ILunaA/MWS/20170422_MWStrip/Screenshot_2017-04-23-11-54-00.jpeg

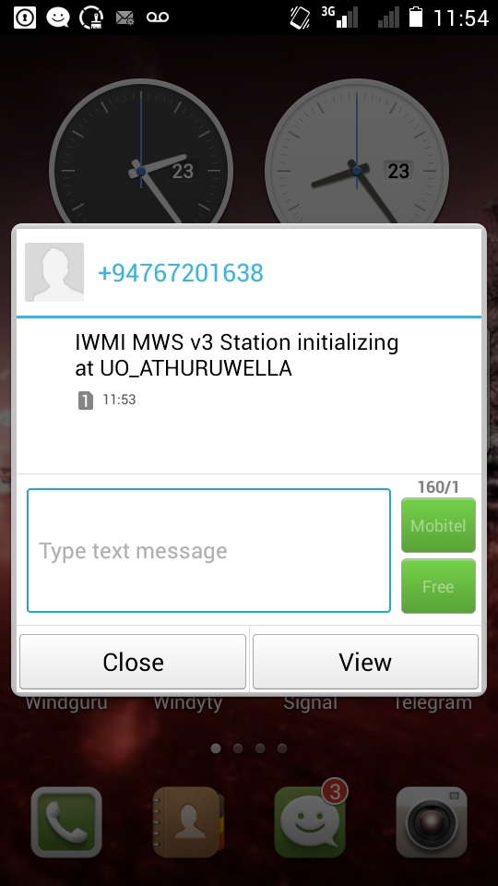
20170422_MWStrip/Screenshot_2017-04-23-11-54-00.jpeg
