ILunaA/MWS/20170422_MWStrip/Screenshot_2017-04-25-07-33-01.jpeg

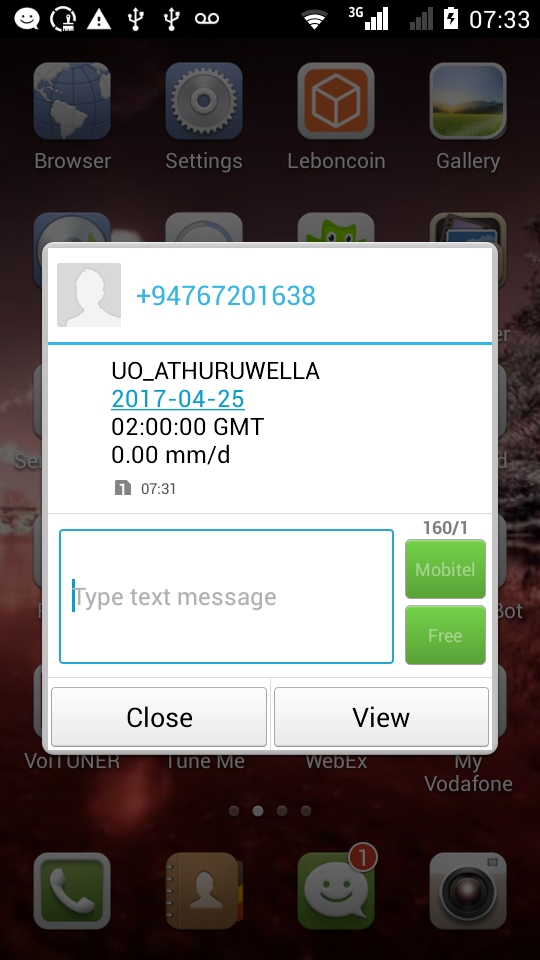
20170422_MWStrip/Screenshot_2017-04-25-07-33-01.jpeg
