ILunaA/MWS/20170422_MWStrip/Screenshot_2017-04-25-11-26-05.jpeg

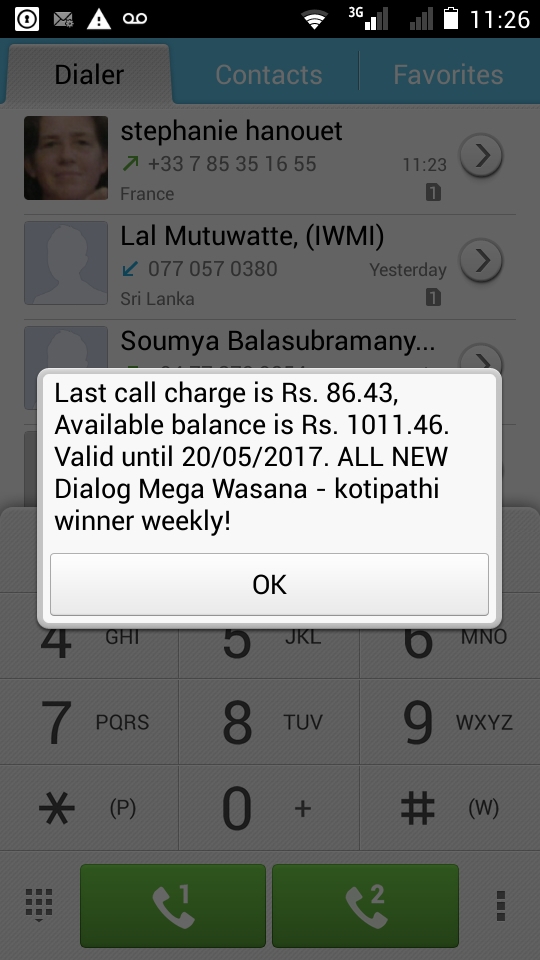
20170422_MWStrip/Screenshot_2017-04-25-11-26-05.jpeg
