ILunaA/MWS/20170422_MWStrip/Screenshot_2017-04-25-14-49-04.jpeg

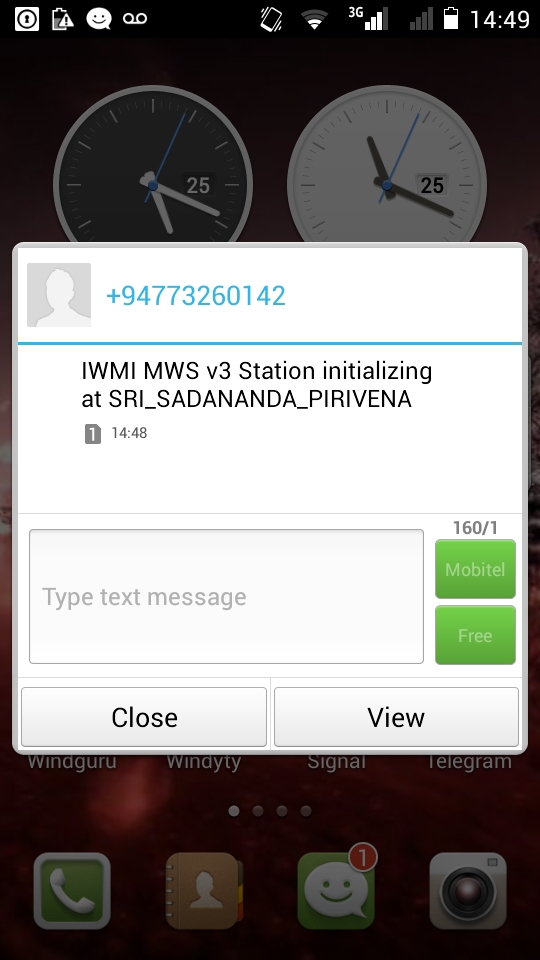
20170422_MWStrip/Screenshot_2017-04-25-14-49-04.jpeg
