ILunaA/MWS/20170422_MWStrip/Screenshot_2017-04-25-15-38-25.jpeg

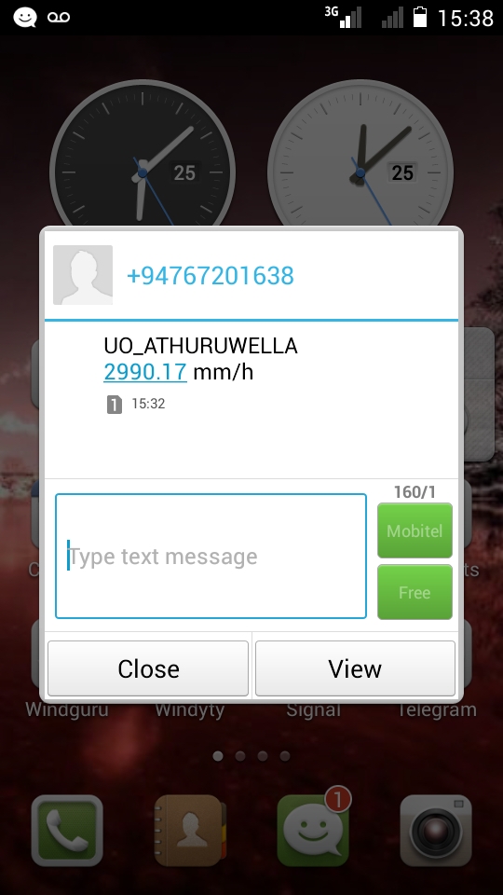
20170422_MWStrip/Screenshot_2017-04-25-15-38-25.jpeg
