ILunaA/MWS/20170422_MWStrip/Screenshot_2017-04-25-21-17-44.jpeg

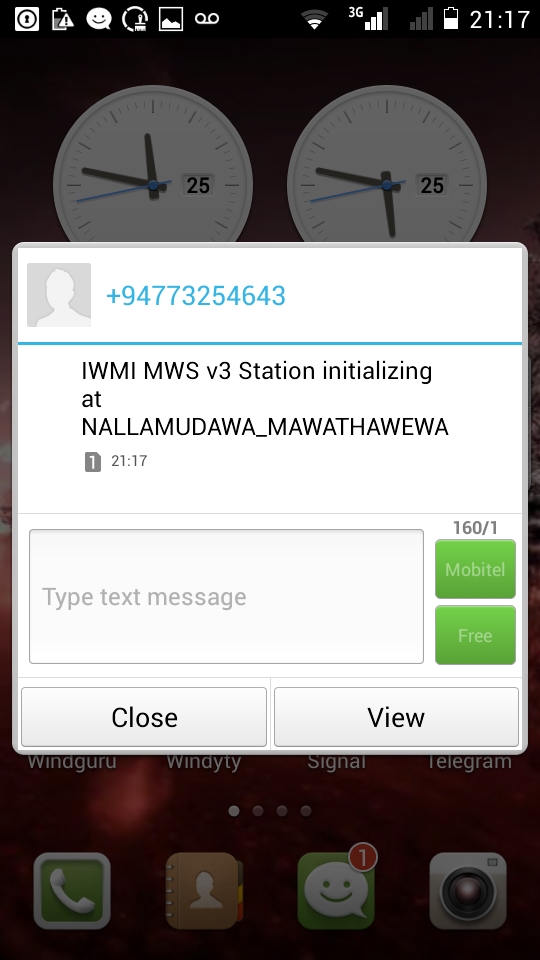
20170422_MWStrip/Screenshot_2017-04-25-21-17-44.jpeg
