ILunaA/MWS/DATA/UO_PALAYAKULAMA/MWSDataAnalysis.png

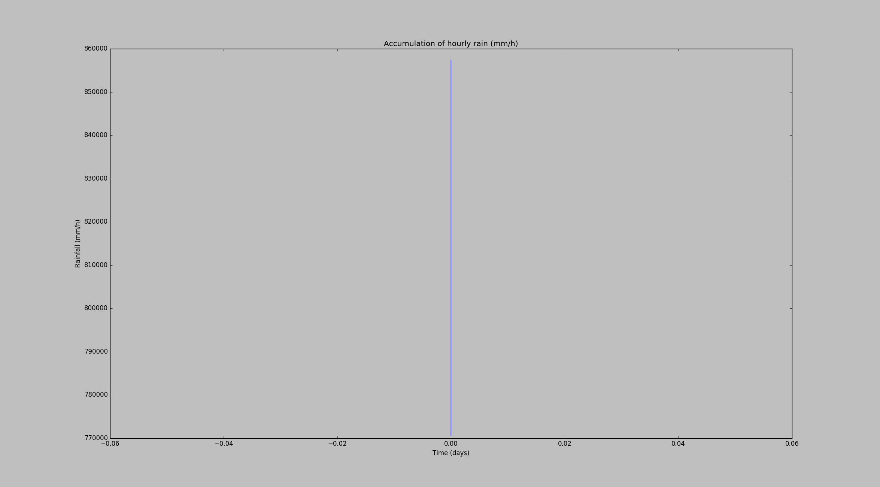
DATA/UO_PALAYAKULAMA/MWSDataAnalysis.png
