ILunaA/MWS/OSHW/radiationshield/Screen Shot 2015-04-08 at 9.11.47 PM.png

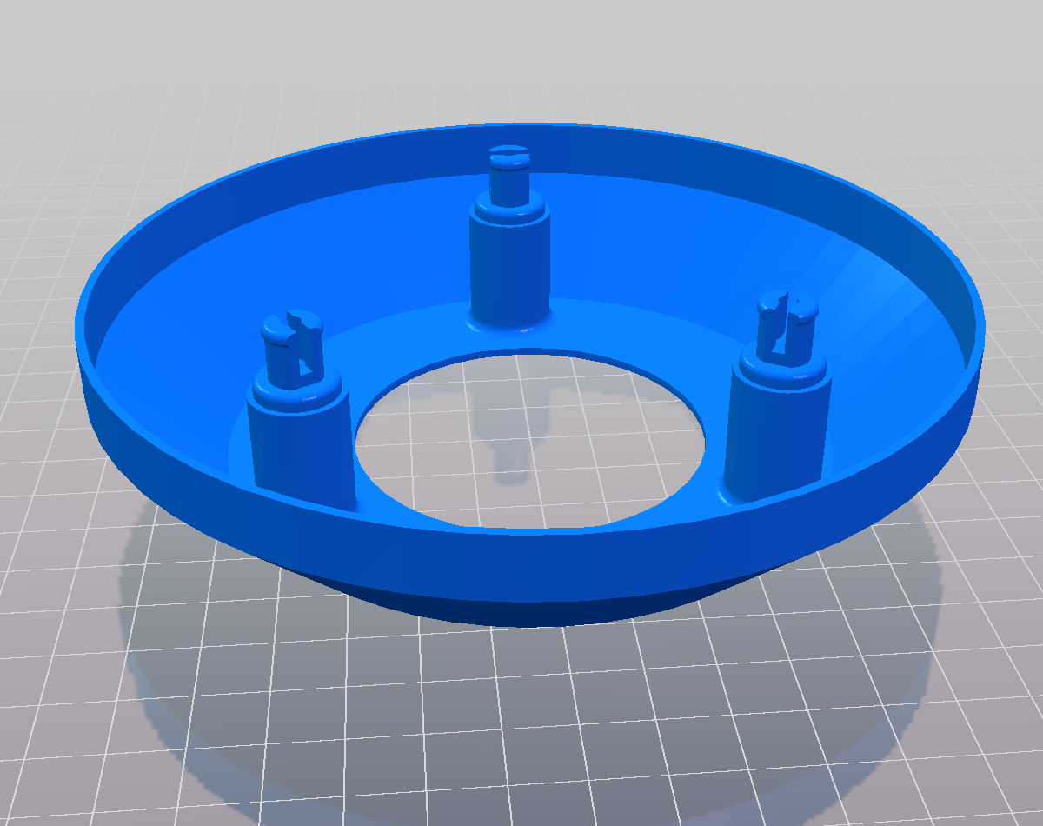
OSHW/radiationshield/Screen Shot 2015-04-08 at 9.11.47 PM.png
