ILunaA/MWS/OSHW/radiationshield/Screen Shot 2015-04-08 at 9.12.31 PM.png

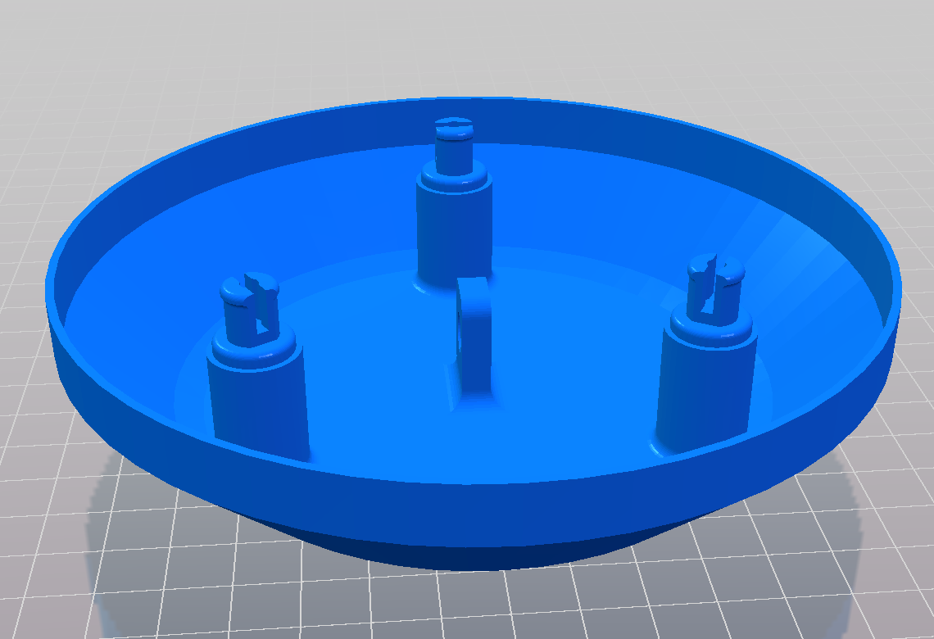
OSHW/radiationshield/Screen Shot 2015-04-08 at 9.12.31 PM.png
