ILunaA/MWS/OSHW/raingauge2/rainmeter_display_large_preview_featured.jpg

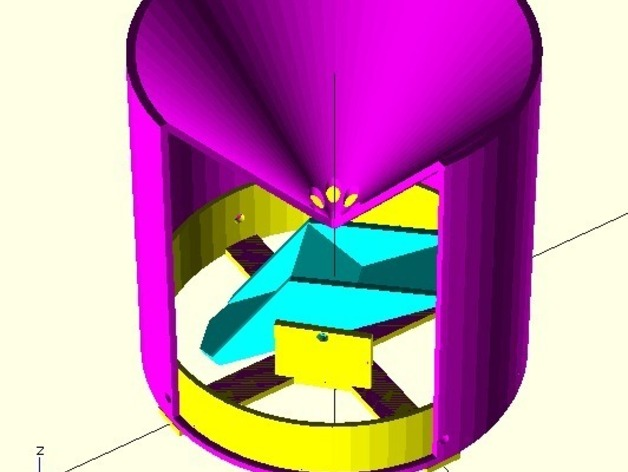
OSHW/raingauge2/rainmeter_display_large_preview_featured.jpg
