ILunaA/MWS/OSHW/raingauge2/rainmeter_plate_lowres_preview_featured.jpg

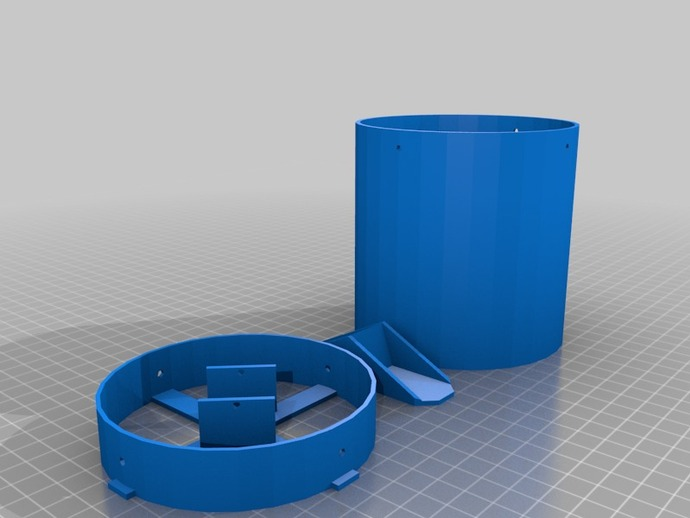
OSHW/raingauge2/rainmeter_plate_lowres_preview_featured.jpg
