ILunaA/MWS/OSHW/raingauge2/rainmeter_preview_featured.jpg

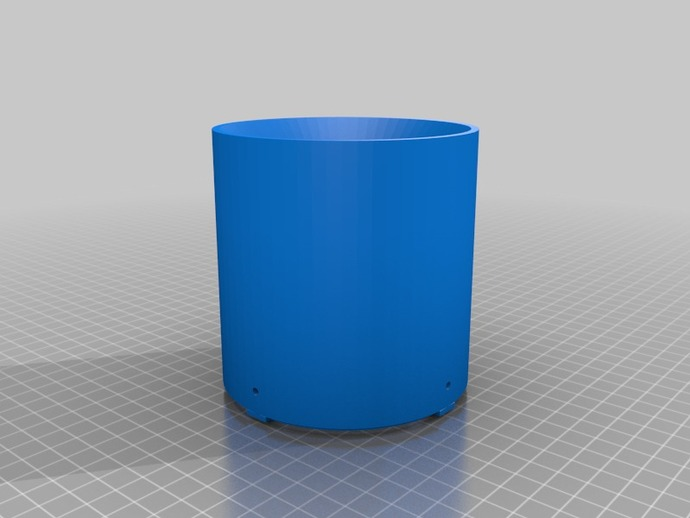
OSHW/raingauge2/rainmeter_preview_featured.jpg
