ILunaA/MWS/OSHW/raingauge3_windspeed/Screenshot from 2016-06-08 13-36-43.png

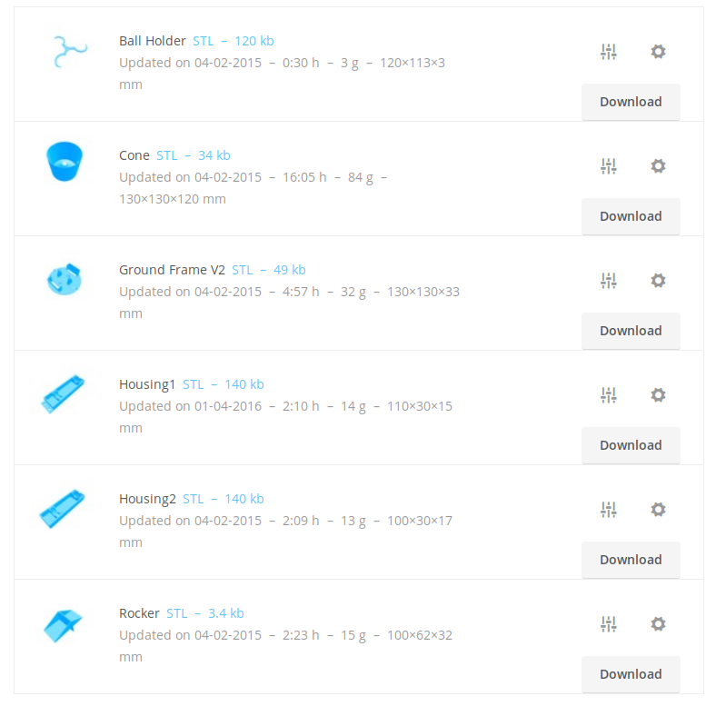
OSHW/raingauge3_windspeed/Screenshot from 2016-06-08 13-36-43.png
