ILunaA/MWS/OSHW/raingauge/Assem2round2.JPG

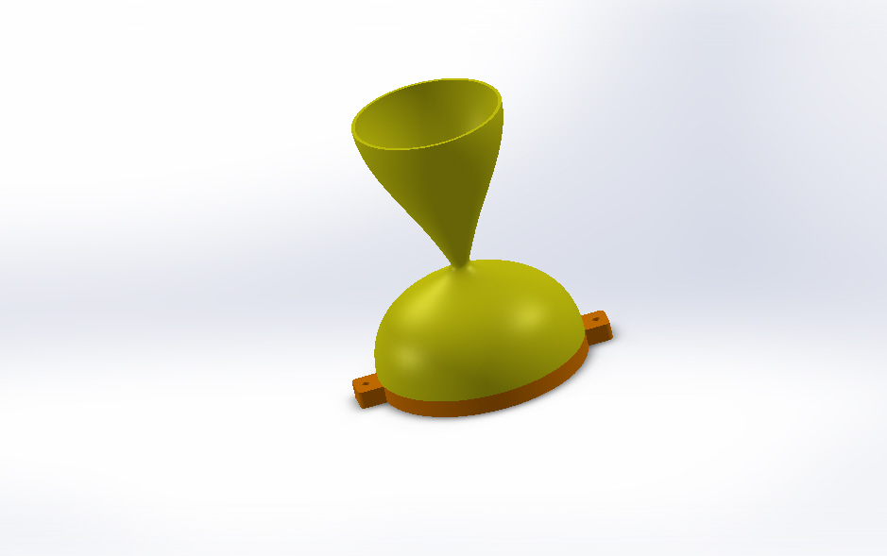
OSHW/raingauge/Assem2round2.JPG
