ILunaA/MWS/OSHW/raingauge/base-round.JPG

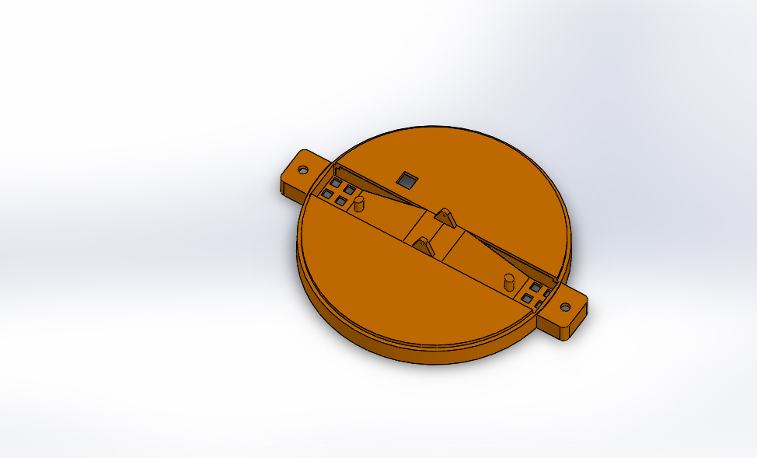
OSHW/raingauge/base-round.JPG
