ILunaA/MWS/OSHW/raingauge/collector - Copyround.JPG

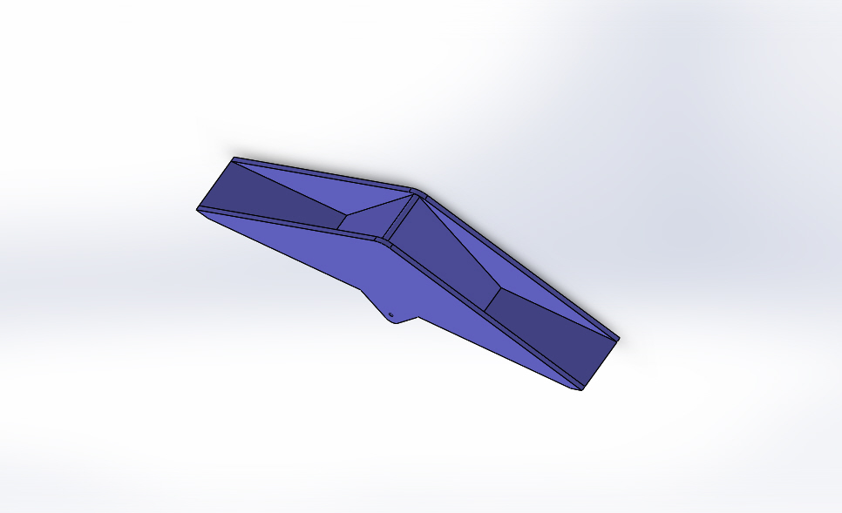
OSHW/raingauge/collector - Copyround.JPG
