ILunaA/MWS/OSHW/raingauge/Cover-round1.JPG

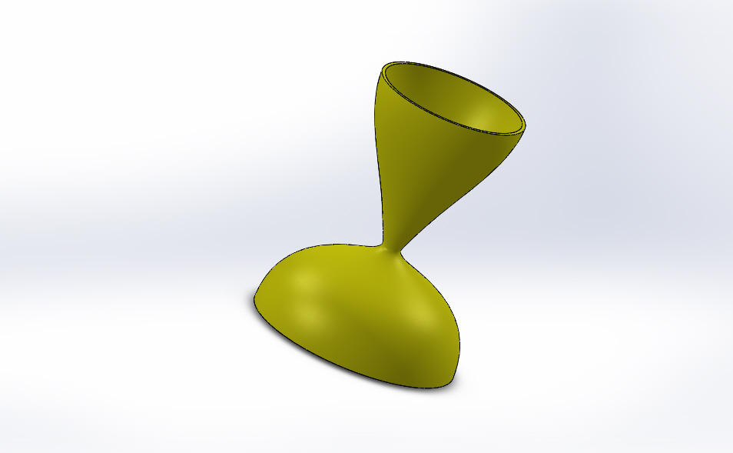
OSHW/raingauge/Cover-round1.JPG
