ILunaA/MWS/OSHW/raingauge/Cover-round.JPG

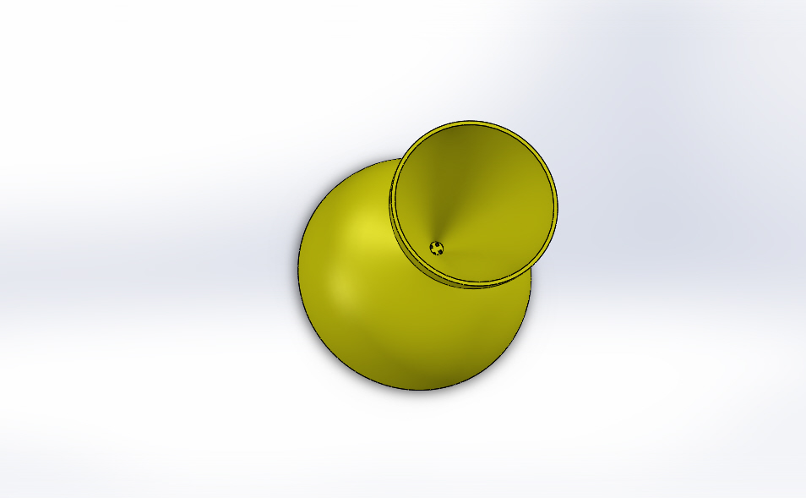
OSHW/raingauge/Cover-round.JPG
