ILunaA/MWS/OSHW/raingauge3_windspeed/ground_frame_v2.stl

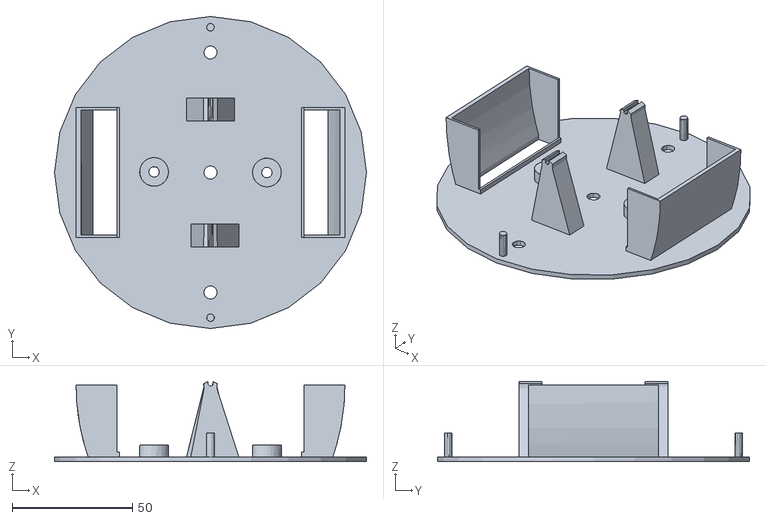
[picture p48: CAD file, 2016-06-08]
OSHW/raingauge3_windspeed/ground_frame_v2.stl
130.0 x 130.0 x 33.4
