ILunaA/MWS/OSHW/raingauge4/files/Outer_Body.stl

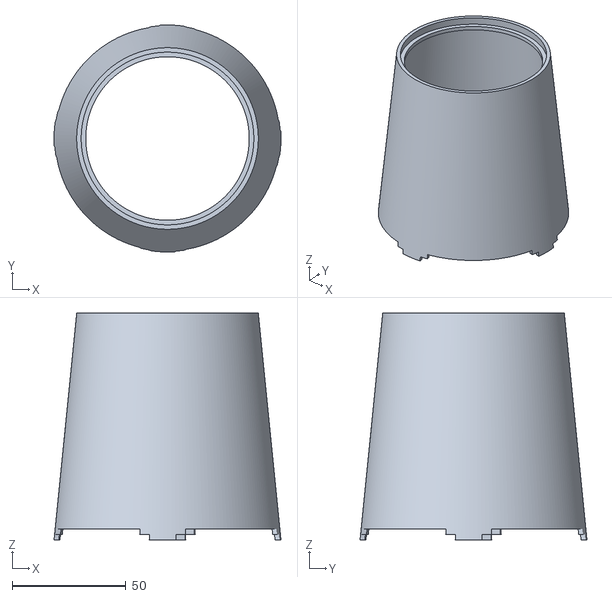
[picture p49: CAD file, 2017-03-09]
OSHW/raingauge4/files/Outer_Body.stl
100.0 x 100.0 x 100.0
