ILunaA/MWS/OSHW/Pluviometro/BOTTOM CAP.SLDPRT

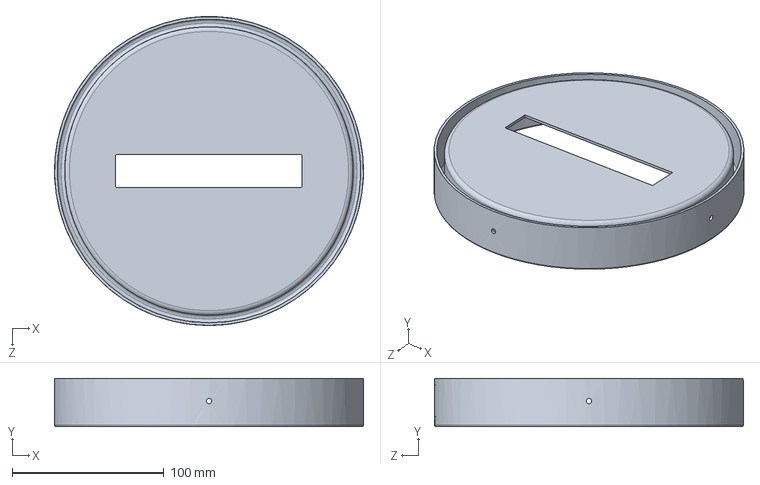
[picture p50: CAD file, 2017-05-09]
OSHW/Pluviometro/BOTTOM CAP.SLDPRT
203.6 x 31.8 x 203.6 mm
