ILunaA/MWS/OSHW/radiationshield1/Radiation_Shield_For_Weather_Station_Temperature_Humidity/Rad_Shd_Fin_V1.stl

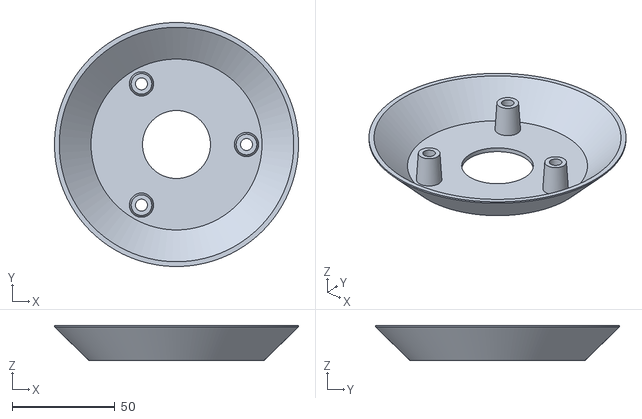
[picture p51: CAD file, 2016-03-31]
OSHW/radiationshield1/Radiation_Shield_For_Weather_Station_Temperature_Humidity/Rad_Shd_Fin_V1.stl
118.5 x 118.5 x 17.0
