ILunaA/MWS/OSHW/raingauge/base-round.SLDPRT

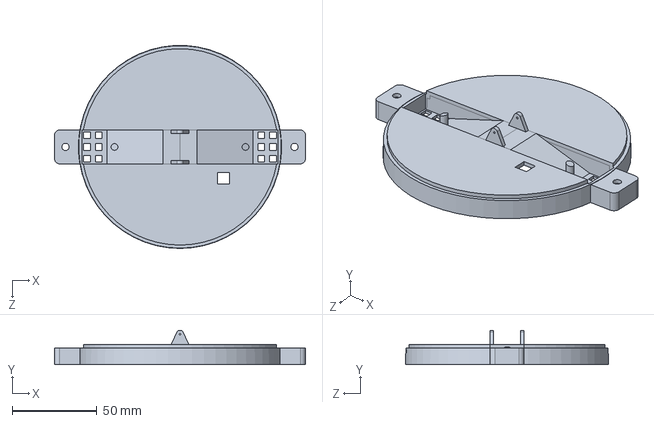
[picture p52: CAD file, 2015-03-08]
OSHW/raingauge/base-round.SLDPRT
148.3 x 20.4 x 119.9 mm
