ILunaA/MWS/OSHW/raingauge1/rain_base2.stl

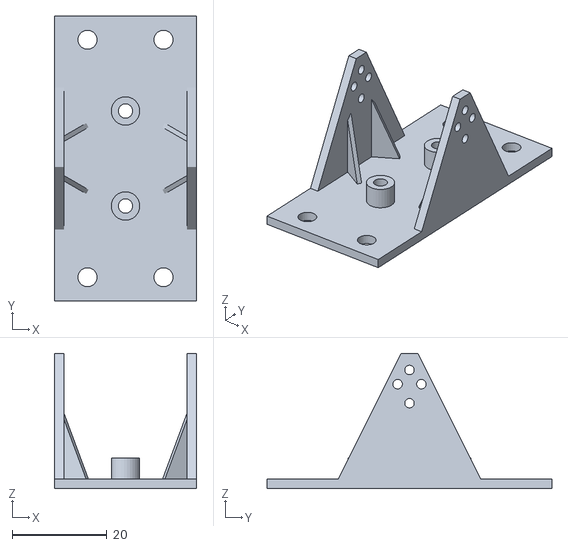
[picture p53: CAD file, 2015-04-08]
OSHW/raingauge1/rain_base2.stl
30.0 x 60.0 x 28.5
