ILunaA/MWS/OSHW/raingauge3_windspeed/cone.stl

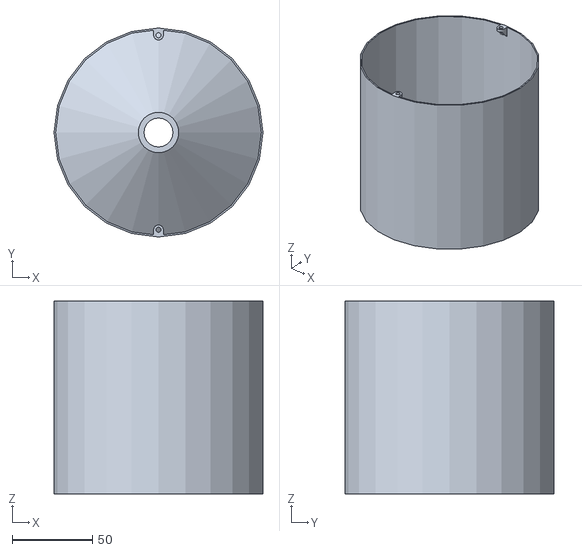
[picture p54: CAD file, 2016-06-08]
OSHW/raingauge3_windspeed/cone.stl
130.0 x 130.0 x 120.0
