ILunaA/MWS/OSHW/raingauge4/files/Funnel.stl

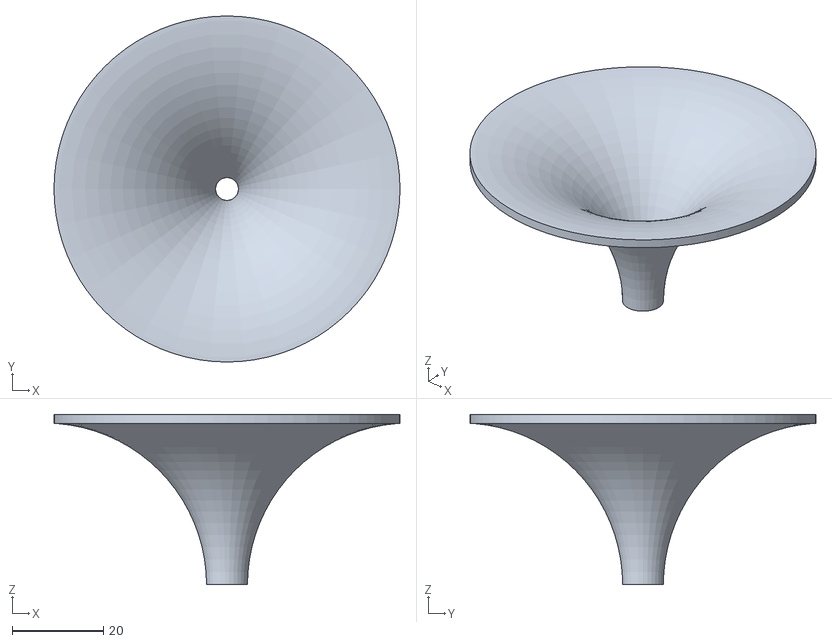
[picture p55: CAD file, 2017-03-09]
OSHW/raingauge4/files/Funnel.stl
76.0 x 76.0 x 37.4
