ILunaA/MWS/OSHW/Pluviometro/Tic.SLDPRT

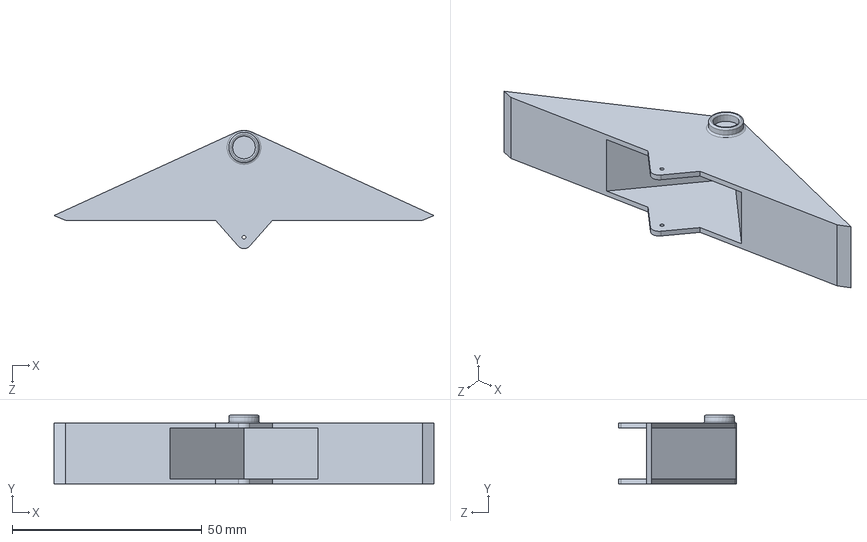
[picture p56: CAD file, 2017-05-09]
OSHW/Pluviometro/Tic.SLDPRT
100.0 x 18.1 x 31.1 mm
