ILunaA/MWS/OSHW/radiationshield1/Radiation_Shield_For_Weather_Station_Temperature_Humidity/AM2315_mount_V1.stl

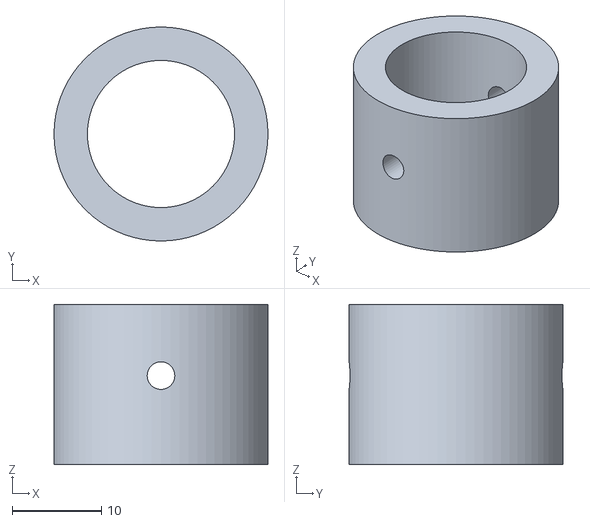
[picture p57: CAD file, 2016-03-31]
OSHW/radiationshield1/Radiation_Shield_For_Weather_Station_Temperature_Humidity/AM2315_mount_V1.stl
24.0 x 24.0 x 18.0
