ILunaA/MWS/OSHW/raingauge/Assem2.STEP

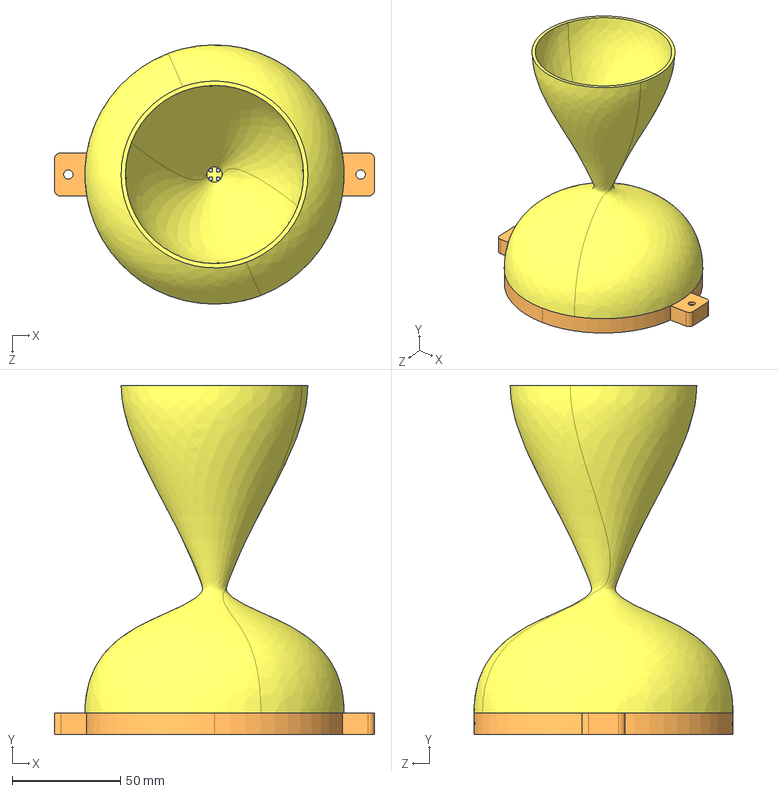
[picture p58: CAD file, 2015-03-08]
OSHW/raingauge/Assem2.STEP
148.3 x 161.5 x 120.0 mm
base-round
collector - Copy
Cover-round
