ILunaA/MWS/OSHW/raingauge1/Base3.stl

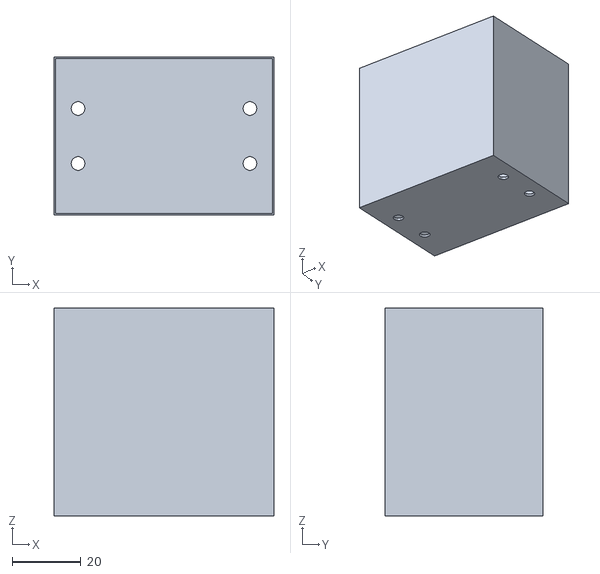
[picture p59: CAD file, 2015-04-08]
OSHW/raingauge1/Base3.stl
64.0 x 46.0 x 60.5
