ILunaA/MWS/OSHW/raingauge3_windspeed/ball_holder.stl

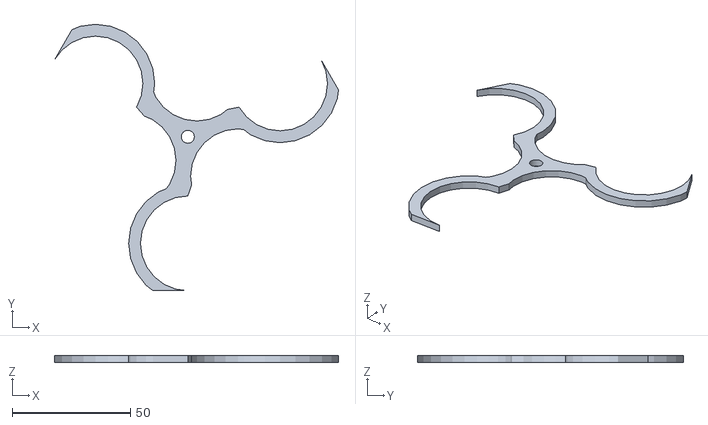
[picture p60: CAD file, 2016-06-08]
OSHW/raingauge3_windspeed/ball_holder.stl
119.9 x 112.5 x 3.00
