ILunaA/MWS/OSHW/raingauge4/files/Base.stl

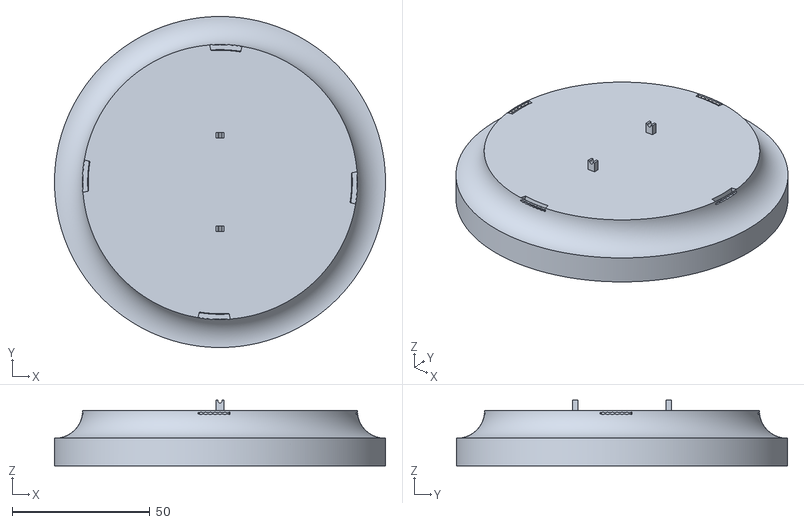
[picture p61: CAD file, 2017-03-09]
OSHW/raingauge4/files/Base.stl
120.0 x 120.0 x 23.8
