ILunaA/MWS/OSHW/radiationshield1/Radiation_Shield_For_Weather_Station_Temperature_Humidity/Rad_Shd_Horz_mount_V1.stl

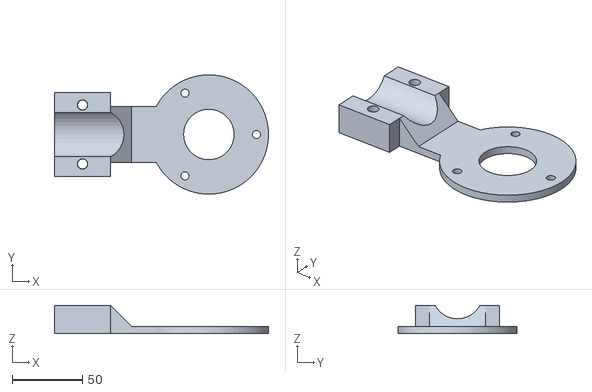
[picture p62: CAD file, 2016-03-31]
OSHW/radiationshield1/Radiation_Shield_For_Weather_Station_Temperature_Humidity/Rad_Shd_Horz_mount_V1.stl
152.5 x 85.0 x 20.0
