ILunaA/MWS/OSHW/raingauge3_windspeed/housing1.stl

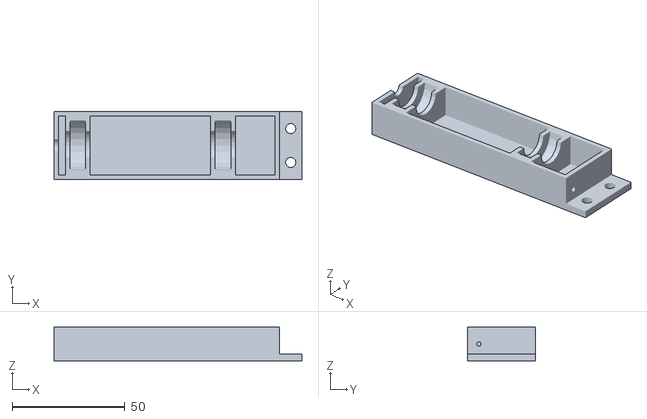
[picture p63: CAD file, 2016-06-08]
OSHW/raingauge3_windspeed/housing1.stl
110.0 x 30.0 x 15.0
