ILunaA/MWS/OSHW/Pluviometro/SPACER.SLDPRT

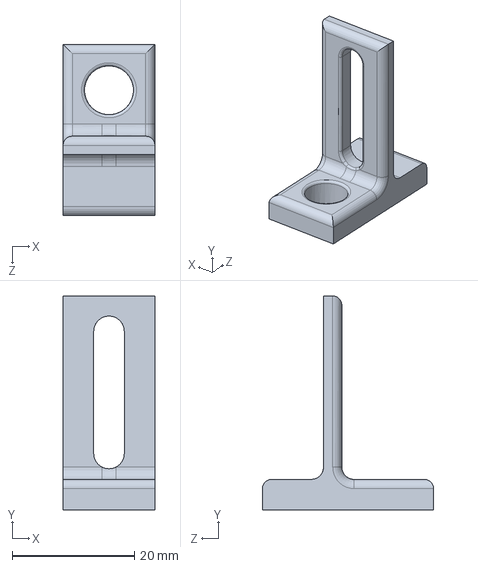
[picture p64: CAD file, 2017-05-09]
OSHW/Pluviometro/SPACER.SLDPRT
15.0 x 35.0 x 28.0 mm
