ILunaA/MWS/OSHW/radiationshield1/Radiation_Shield_For_Weather_Station_Temperature_Humidity/SHT15_mount_V1.stl

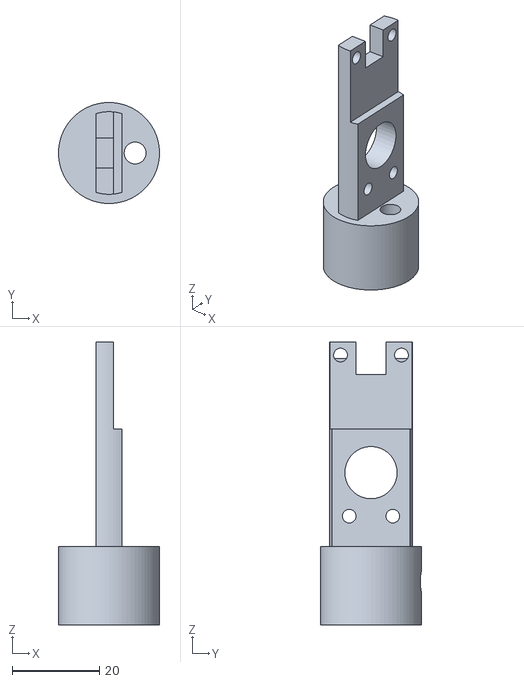
[picture p65: CAD file, 2016-03-31]
OSHW/radiationshield1/Radiation_Shield_For_Weather_Station_Temperature_Humidity/SHT15_mount_V1.stl
23.2 x 23.2 x 65.0
