ILunaA/MWS/OSHW/raingauge3_windspeed/rocker.stl

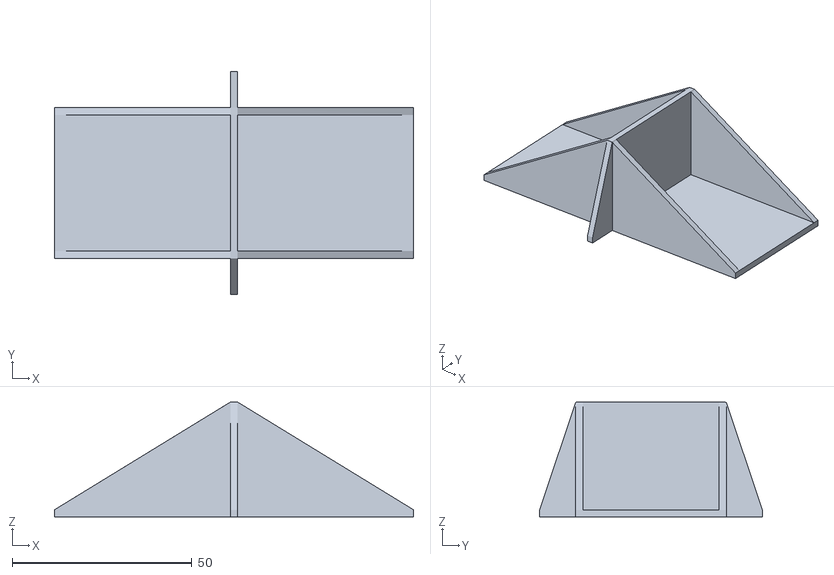
[picture p66: CAD file, 2016-06-08]
OSHW/raingauge3_windspeed/rocker.stl
100.0 x 62.0 x 32.0
