ILunaA/MWS/OSHW/Pluviometro/SUPPORT.SLDPRT

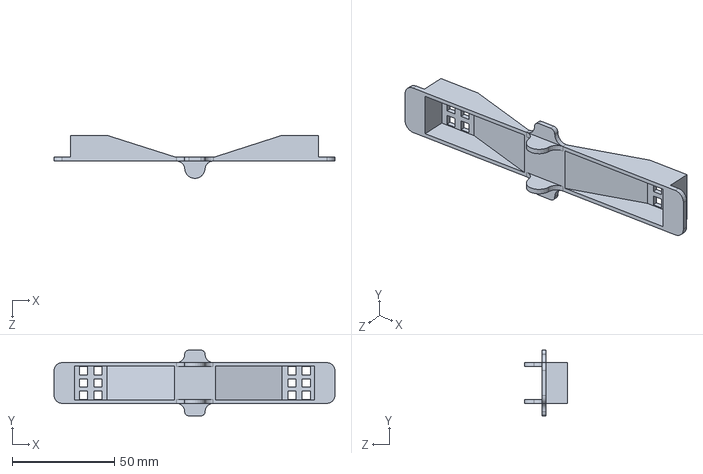
[picture p67: CAD file, 2017-05-09]
OSHW/Pluviometro/SUPPORT.SLDPRT
137.6 x 32.2 x 21.0 mm
