ILunaA/MWS/OSHW/radiationshield1/Radiation_Shield_For_Weather_Station_Temperature_Humidity/HTU21D_mount_V1.stl

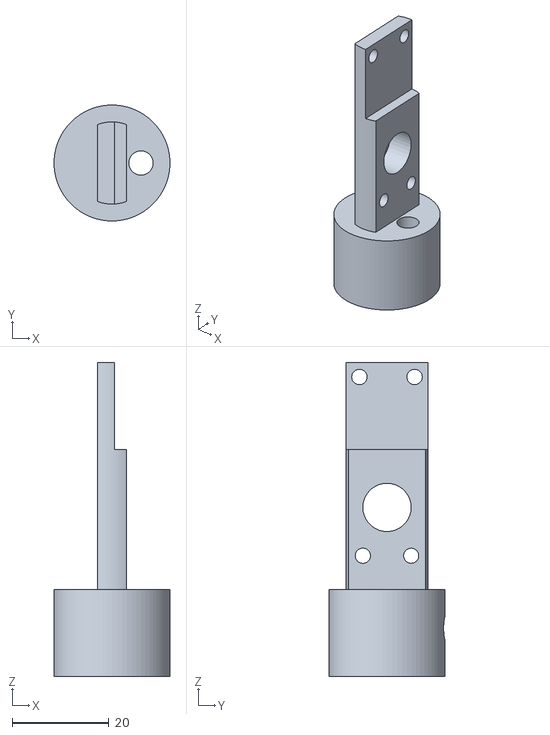
[picture p68: CAD file, 2016-03-31]
OSHW/radiationshield1/Radiation_Shield_For_Weather_Station_Temperature_Humidity/HTU21D_mount_V1.stl
24.0 x 24.0 x 65.0
