ILunaA/MWS/OSHW/radiationshield1/Radiation_Shield_For_Weather_Station_Temperature_Humidity/Rad_Shd_Base_V1.stl

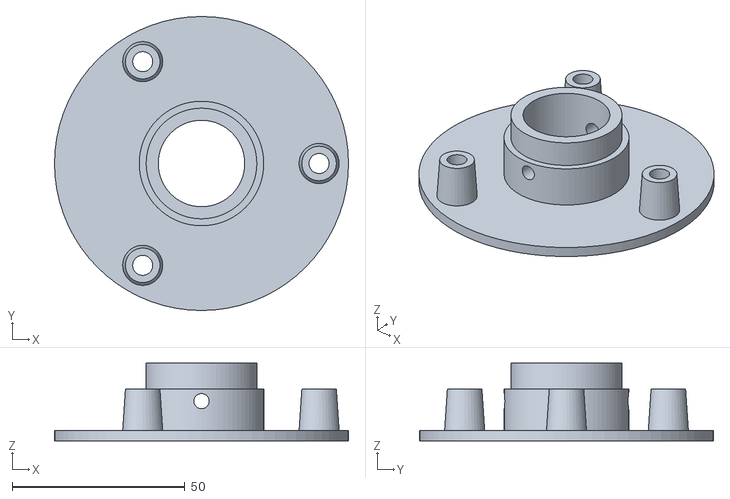
[picture p69: CAD file, 2016-03-31]
OSHW/radiationshield1/Radiation_Shield_For_Weather_Station_Temperature_Humidity/Rad_Shd_Base_V1.stl
85.0 x 85.0 x 22.5
